Dennis-van-Gils/PCB-resistive-AC-soil-moisture-sensor/LTspice_simulation/SMX_simulation.asc

C1: cap; 0.1µ
C2: cap; 2.2µ
C3: cap; 2.2µ
C4: cap; 3.3µ
C5: cap; 2.2µ
R1: res; 150k
R2: res; 390
R3: res; 53.6k
R4: res; 1k
R5: res; 10k
R6: res; 4.7k
U1: NE555
V1: voltage; 3
Named nets: red, green, white, black, 0
.step oct param R 1 10e6 10
.op 0 1 0 0.01
.tran 0 0.05 0 1e-6
