Dennis-van-Gils/PCB-resistive-AC-soil-moisture-sensor/LTspice_simulation/SMX_simulation_v3.asc

C1: cap; 0.1µ
C2: cap; 4.7µ
C3: cap; 4.7µ
R1: res; 150k
R2: res; 390
R5: res; 10000
R6: res; 4.7k
R7: res; 100
U1: NE555
V1: voltage; 5
Named nets: red, black, green, 0, OUT
.step oct param R 1 10e6 10
.op 0 1 0 0.01
.tran 0 0.1 0 1e-6
.meas TRAN period TRIG V(OUT)=0.5 TD=10m RISE=1 TARG V(OUT)=0.5 TD=10m RISE=2
.meas TRAN frequency PARAM 1/period
